IowaScaledEngineering/mrbw-wifi/src/include/versions.h

#pragma once

#ifndef MAJOR_VERSION
#define MAJOR_VERSION  0
#endif

#ifndef MINOR_VERSION
#define MINOR_VERSION  0
#endif

#ifndef DELTA_VERSION
#define DELTA_VERSION  1
#endif 

#ifndef GIT_REV
#define GIT_REV    "xxxxxx"
#endif
