IowaScaledEngineering/mrbw-wifi/src-circuitpython/wibridge-python/MRBusThrottle.py

# *************************************************************************
# Title:    Client driver for MRBus Throttle (mainly the ProtoThrottle)
# Authors:  Michael D. Petersen <railfan@drgw.net>
#           Nathan D. Holmes <maverick@drgw.net>
# File:     MRBusThrottle.py
# License:  GNU General Public License v3
# 
# LICENSE:
#   Copyright (C) 2018 Michael Petersen & Nathan Holmes
#     
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
# DESCRIPTION:
#   This class provides a way parse incoming MRBus throttle packets (primarily
#   from the ProtoThrottle ( http://www.protothrottle.com/ ) and send them
#   on to a variety of command stations as a form of protocol translator.
# 
# *************************************************************************

import mrbus
import sys
import time

class MRBusThrottle:
  def __init__(self, addr):
    self.locAddr = 0
    self.locAddrLong = True
    self.locSpeed = 0
    self.locDirection = 0
    self.locObjID = None
    self.locEStop = 0
    self.locFunctions = None
    self.throttleAddr = addr
    self.lastUpdate = 0
    self.debug = False
    return
      
  def getLastUpdateTime(self):
    return self.lastUpdate
   
  def disconnect(self, cmdStn):
    if self.locObjID is not None:
      cmdStn.locomotiveSpeedSet(self.locObjID, 0, 0)
      cmdStn.locomotiveDisconnect(self.locObjID)
      
   
  def update(self, cmdStn, pkt):
    if pkt.cmd != 0x53 or len(pkt.data) != 9:  # Not a status update, bump out
      return
    if self.debug:
      print("MRBusThrottle (0x%02X): UPDATE loco %d" % (self.throttleAddr, self.locAddr))
      
    addr = pkt.data[0] * 256 + pkt.data[1]
    if 0 != (addr & 0x8000):
      self.locAddrLong = False
      addr = addr & 0x007F
    else:
      self.locAddrLong = True
         
    speed = pkt.data[2] & 0x7F
    if 1 == speed:
      speed = 0
      estop = 1
    elif speed > 1:
      estop = 0
      speed = speed - 1
    elif speed == 0:
      estop = 0
      
    if pkt.data[2] & 0x80:
      direction = 0
    else:
      direction = 1

    if addr != self.locAddr or self.locObjID is None:
      try:
        self.locObjID = cmdStn.locomotiveObjectGet(addr, self.throttleAddr, self.locAddrLong)
      except:
        print("MRBusThrottle (0x%02X) - could not acquire locomotive, will retry" % (self.throttleAddr))
        return
      self.locAddr = addr
      self.locFunctions = None  # We changed locomotives, go get new functions
      print("MRBusThrottle (0x%02X): Acquiring new locomotive %d - objID = %s" % (self.throttleAddr, self.locAddr, self.locObjID))
      
    # Only send ESTOP if we just moved into that state
    if estop != self.locEStop and estop == 1:
      print("MRBusThrottle (0x%02X): Set ESTOP loco %d" % (self.throttleAddr, self.locAddr))
      cmdStn.locomotiveEmergencyStop(self.locObjID)

    self.locEStop = estop
    if self.locEStop != 1 and (speed != self.locSpeed or direction != self.locDirection):
      print("MRBusThrottle (0x%02X): Set loco [%d] speed %d %s" % (self.throttleAddr, self.locAddr, speed, ["FWD","REV"][direction]))
      cmdStn.locomotiveSpeedSet(self.locObjID, speed, direction)

    self.locSpeed = speed
    self.locDirection = direction
      
    # On the first pass, get the function statuses from the command station
    # The LNWI / WiThrottle support this, others may in the future
    if self.locFunctions is None:
      try:
        self.locFunctions = cmdStn.locomotiveFunctionsGet(self.locObjID)
        print("MRBusThrottle (0x%02X): Got loco [%d] functions from cmd station\n  [%s]" % (self.throttleAddr, self.locAddr, self.locFunctions))
        print(self.locFunctions)
      except Exception as e:
        print("MRBusThrottle (0x%02X): Exception in locomotiveFunctionsGet() for loco [%d]" % (self.throttleAddr, self.locAddr))
        print(e)
        self.locFunctions = [ 0,0,0,0,0,0,0,0,0,0,0,0,0,0,0,0,0,0,0,0,0,0,0,0,0,0,0,0,0 ]
         
    functions = [ 0,0,0,0,0,0,0,0,0,0,
                  0,0,0,0,0,0,0,0,0,0,
                  0,0,0,0,0,0,0,0,0 ]
      
    for i in range(29):
      if i >= 0 and i < 8:
        if pkt.data[6] & (1<<i):
          functions[i] = 1
      elif i >= 8 and i < 16:
        if pkt.data[5] & (1<<(i-8)):
          functions[i] = 1
      elif i >= 16 and i < 24:
        if pkt.data[4] & (1<<(i-16)):
          functions[i] = 1
      elif i >= 24 and i < 29:
        if pkt.data[3] & (1<<(i-24)):
          functions[i] = 1

    for i in range(29):
      if functions[i] != self.locFunctions[i]:
        print("MRBusThrottle (0x%02X): Set loco [%d] function [%d] to [%d]" % (self.throttleAddr, self.locAddr, i, functions[i]))
        cmdStn.locomotiveFunctionSet(self.locObjID, i, functions[i])

    self.locFunctions = functions
    self.lastUpdate = time.monotonic()
    return
      
